doug7410/nowplaying-appliance/hardware/carrier-board/assembly/render-bottom.png

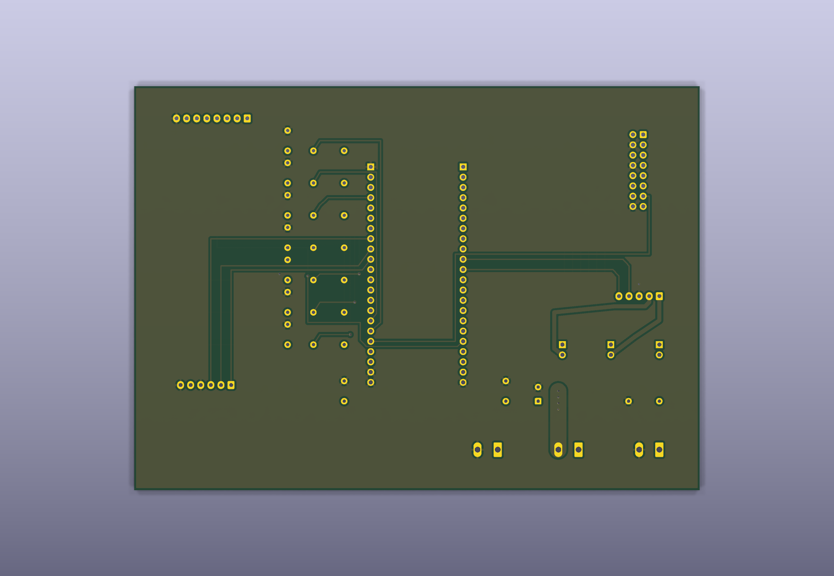
hardware/carrier-board/assembly/render-bottom.png
