doug7410/nowplaying-appliance/hardware/carrier-board/assembly/render-top.png

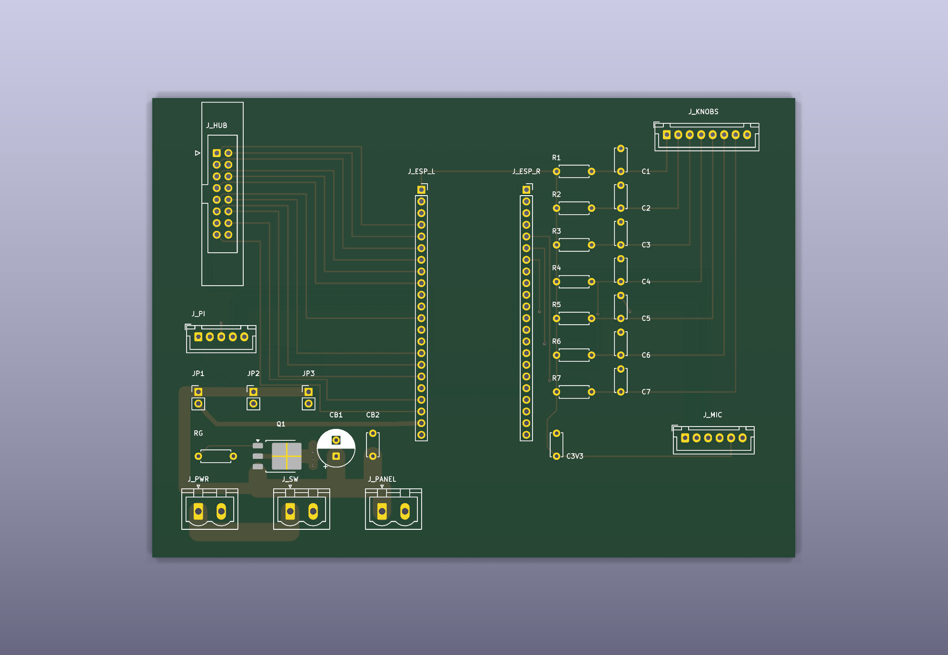
hardware/carrier-board/assembly/render-top.png
