doug7410/nowplaying-appliance/hardware/knob-board/assembly/render-top.png

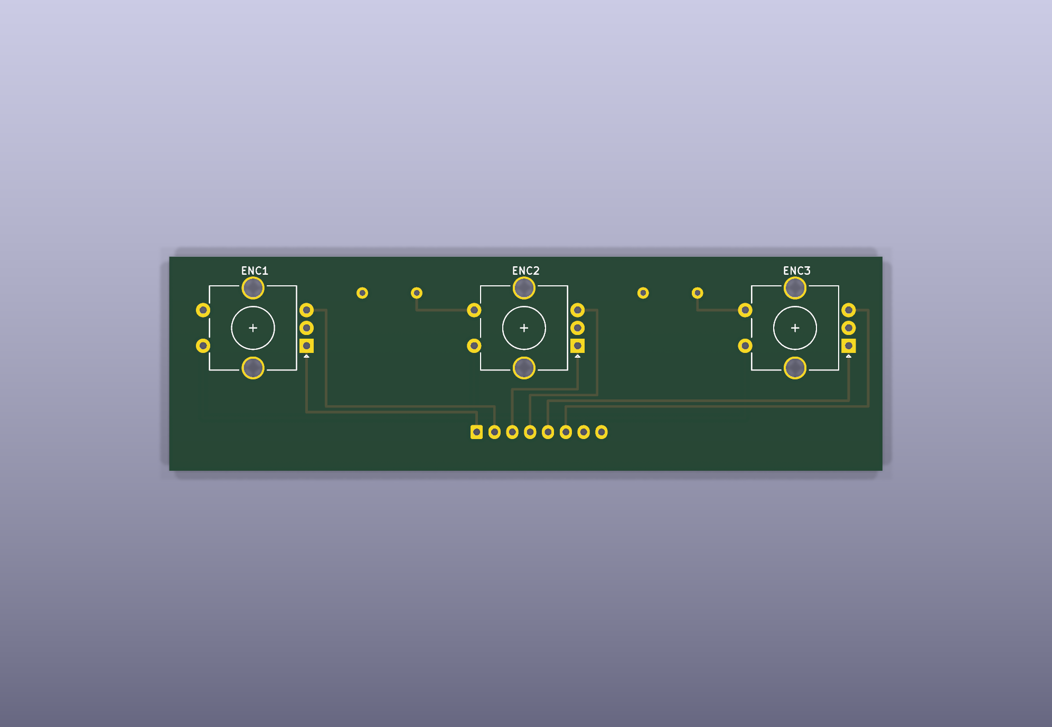
hardware/knob-board/assembly/render-top.png
