doug7410/nowplaying-appliance/hardware/mic-board/assembly/placement-bottom.png

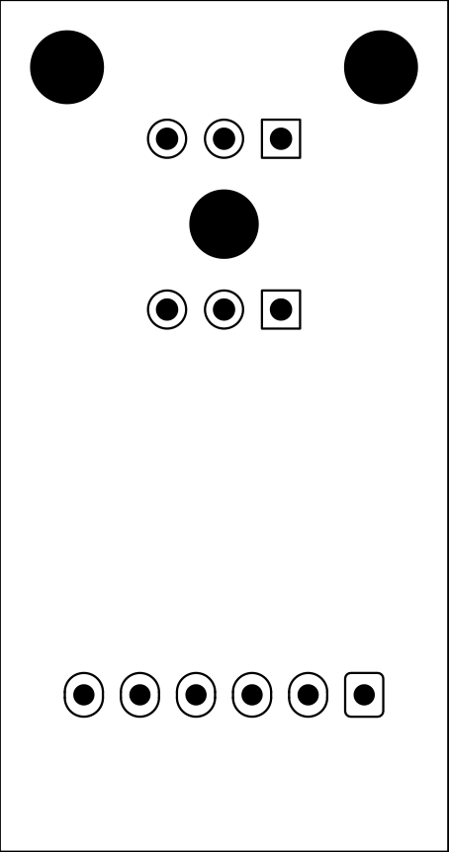
hardware/mic-board/assembly/placement-bottom.png
