doug7410/nowplaying-appliance/hardware/mic-board/assembly/render-bottom.png

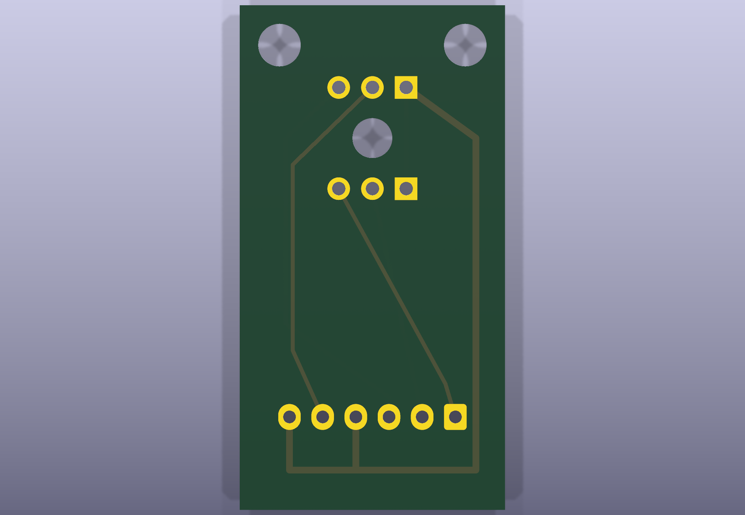
hardware/mic-board/assembly/render-bottom.png
