doug7410/nowplaying-appliance/hardware/mic-board/assembly/render-top.png

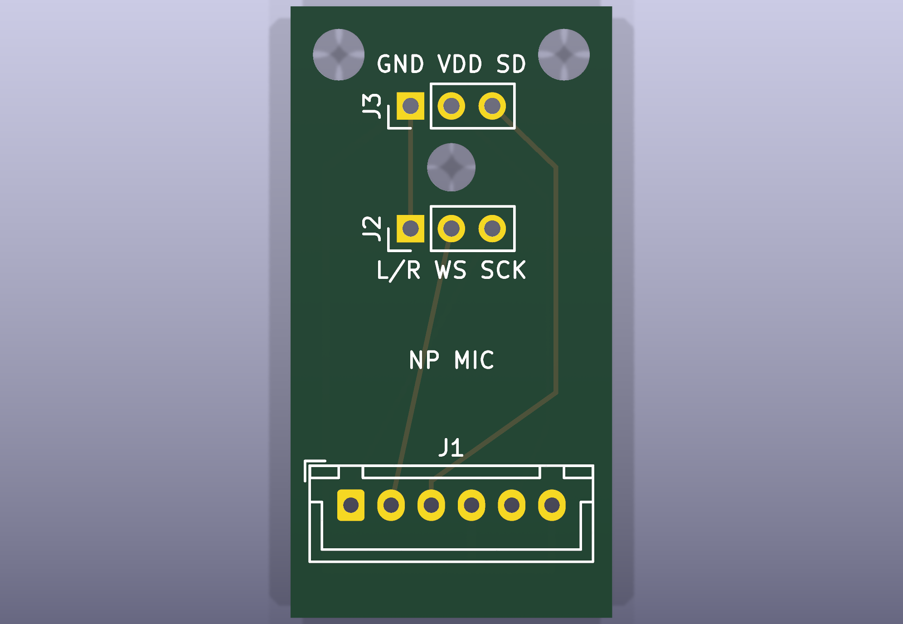
hardware/mic-board/assembly/render-top.png
