doug7410/nowplaying-appliance/hardware/panelboard/assembly/placement-bottom.png

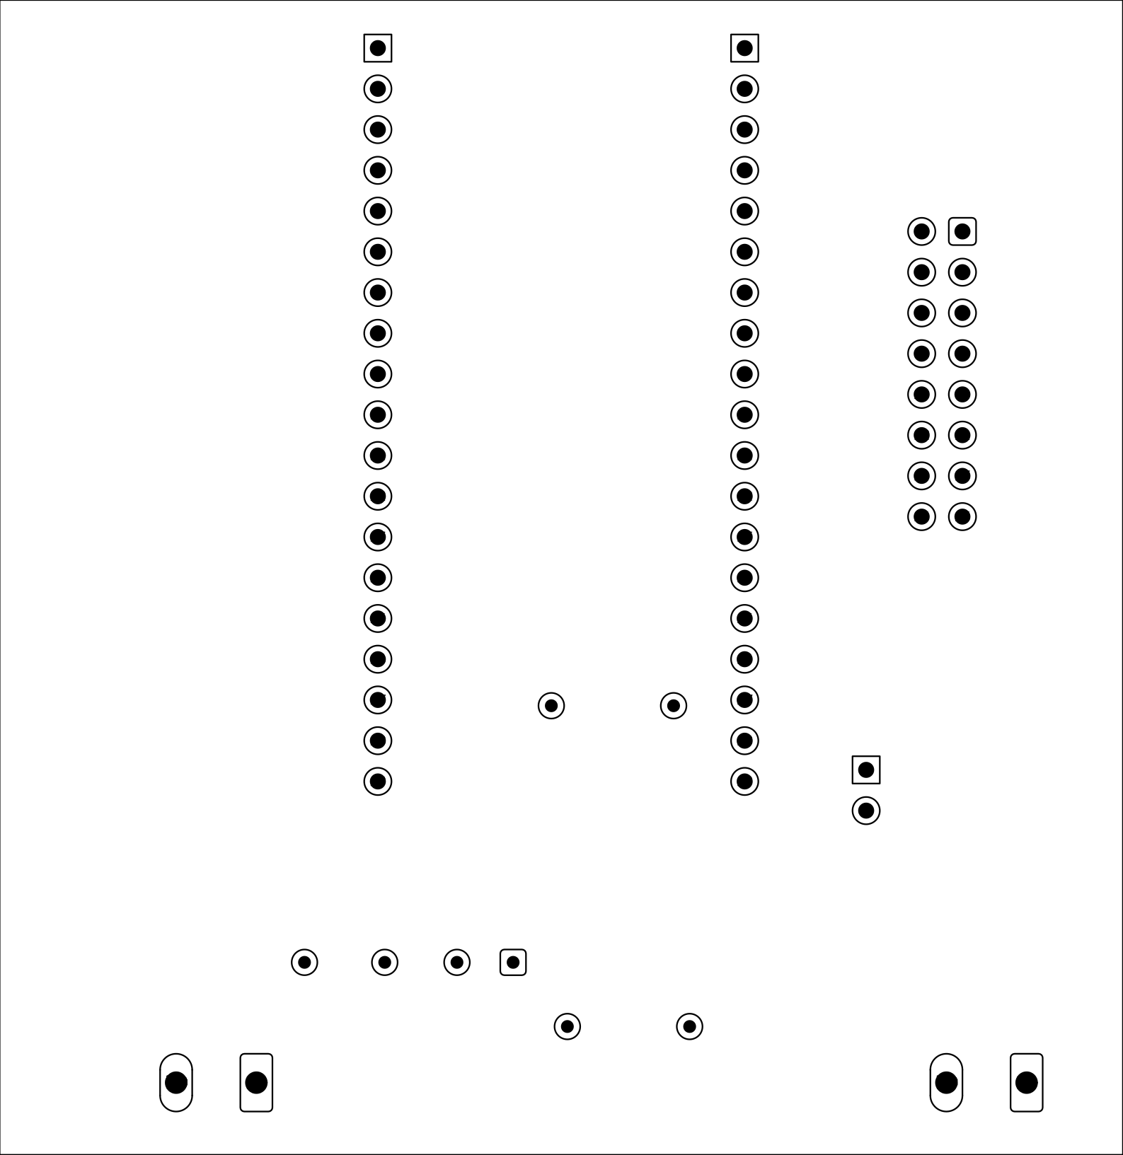
hardware/panelboard/assembly/placement-bottom.png
