doug7410/nowplaying-appliance/hardware/panelboard/assembly/render-bottom.png

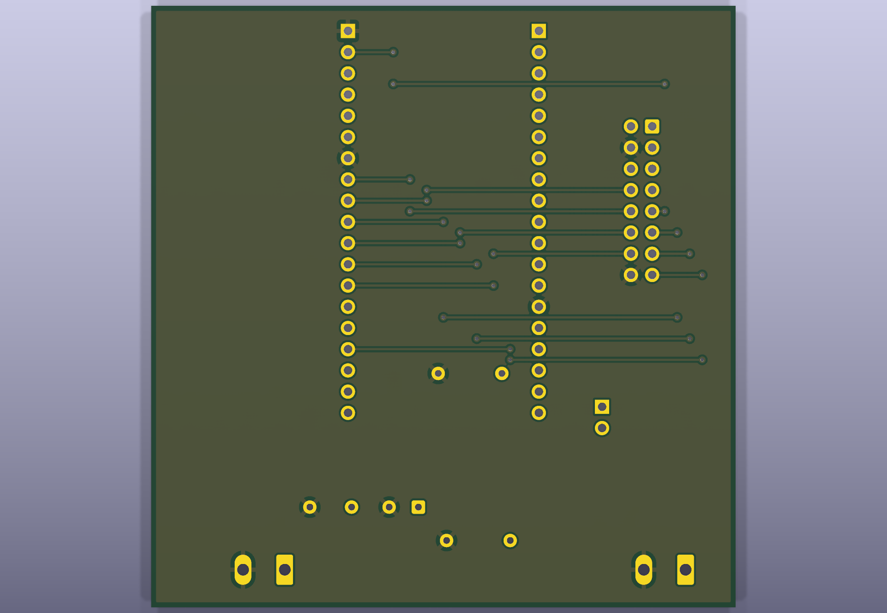
hardware/panelboard/assembly/render-bottom.png
